phorton1/projects-ws2812bSwitchArray1/fusion/w2812bSwitch.png

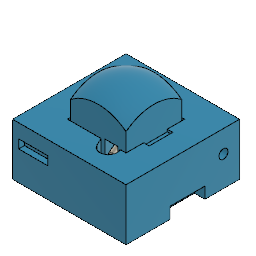
fusion/w2812bSwitch.png
