phorton1/projects-ws2812bSwitchArray1/docs/images/assembly01-wire_dimensions.jpg

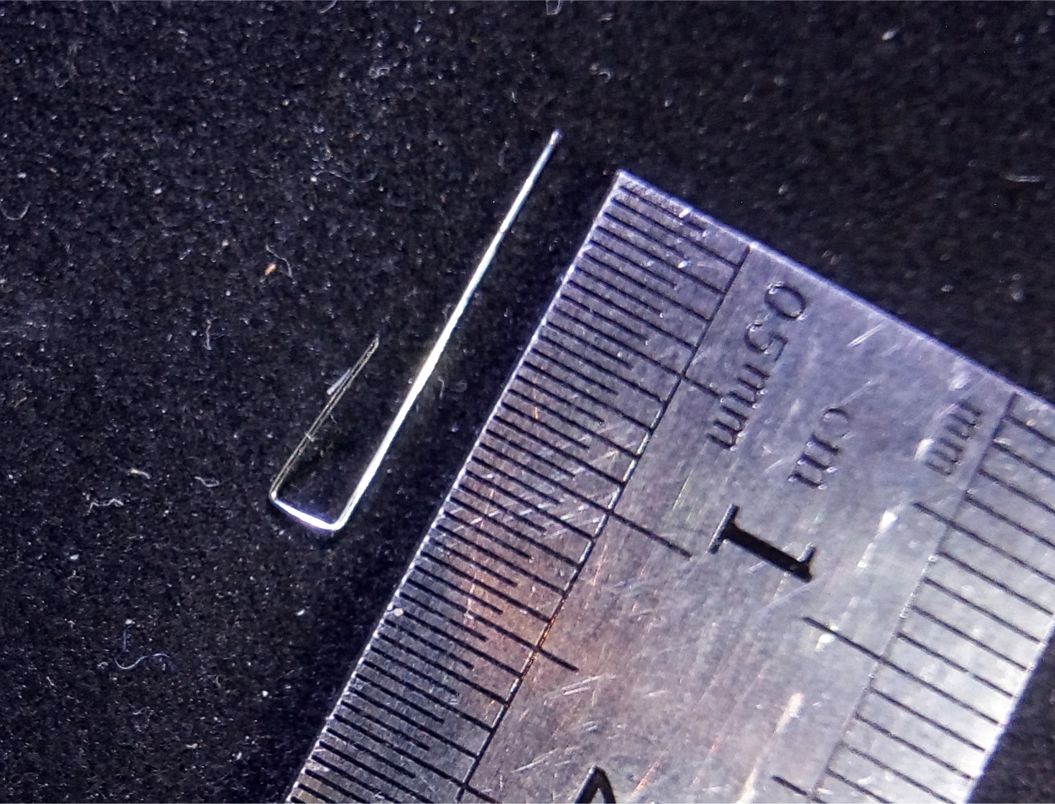
docs/images/assembly01-wire_dimensions.jpg
