phorton1/projects-ws2812bSwitchArray1/docs/images/assembly02-wire_bend.jpg

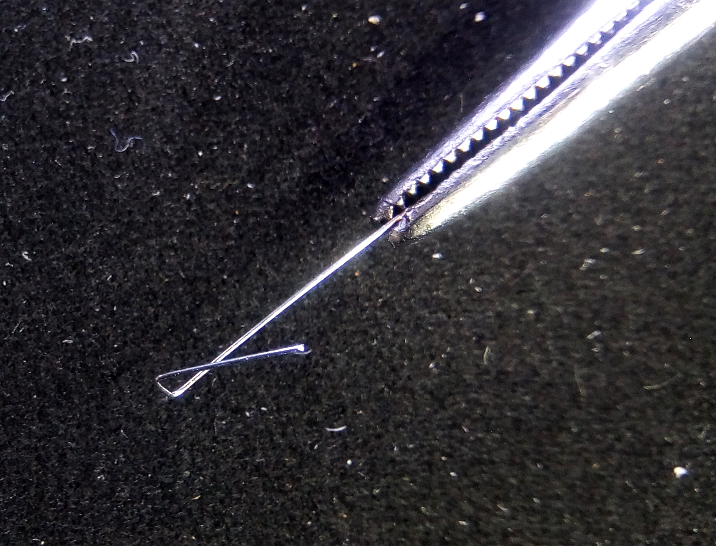
docs/images/assembly02-wire_bend.jpg
